DerSpatz/PCB-reflow-solder-table/HeatTable-Base-v0.9/HeatTable-Base-v0.9.kicad_sch

## KiCad design HeatTable-Base-v0.9/HeatTable-Base-v0.9.kicad_sch (2022-12-29)

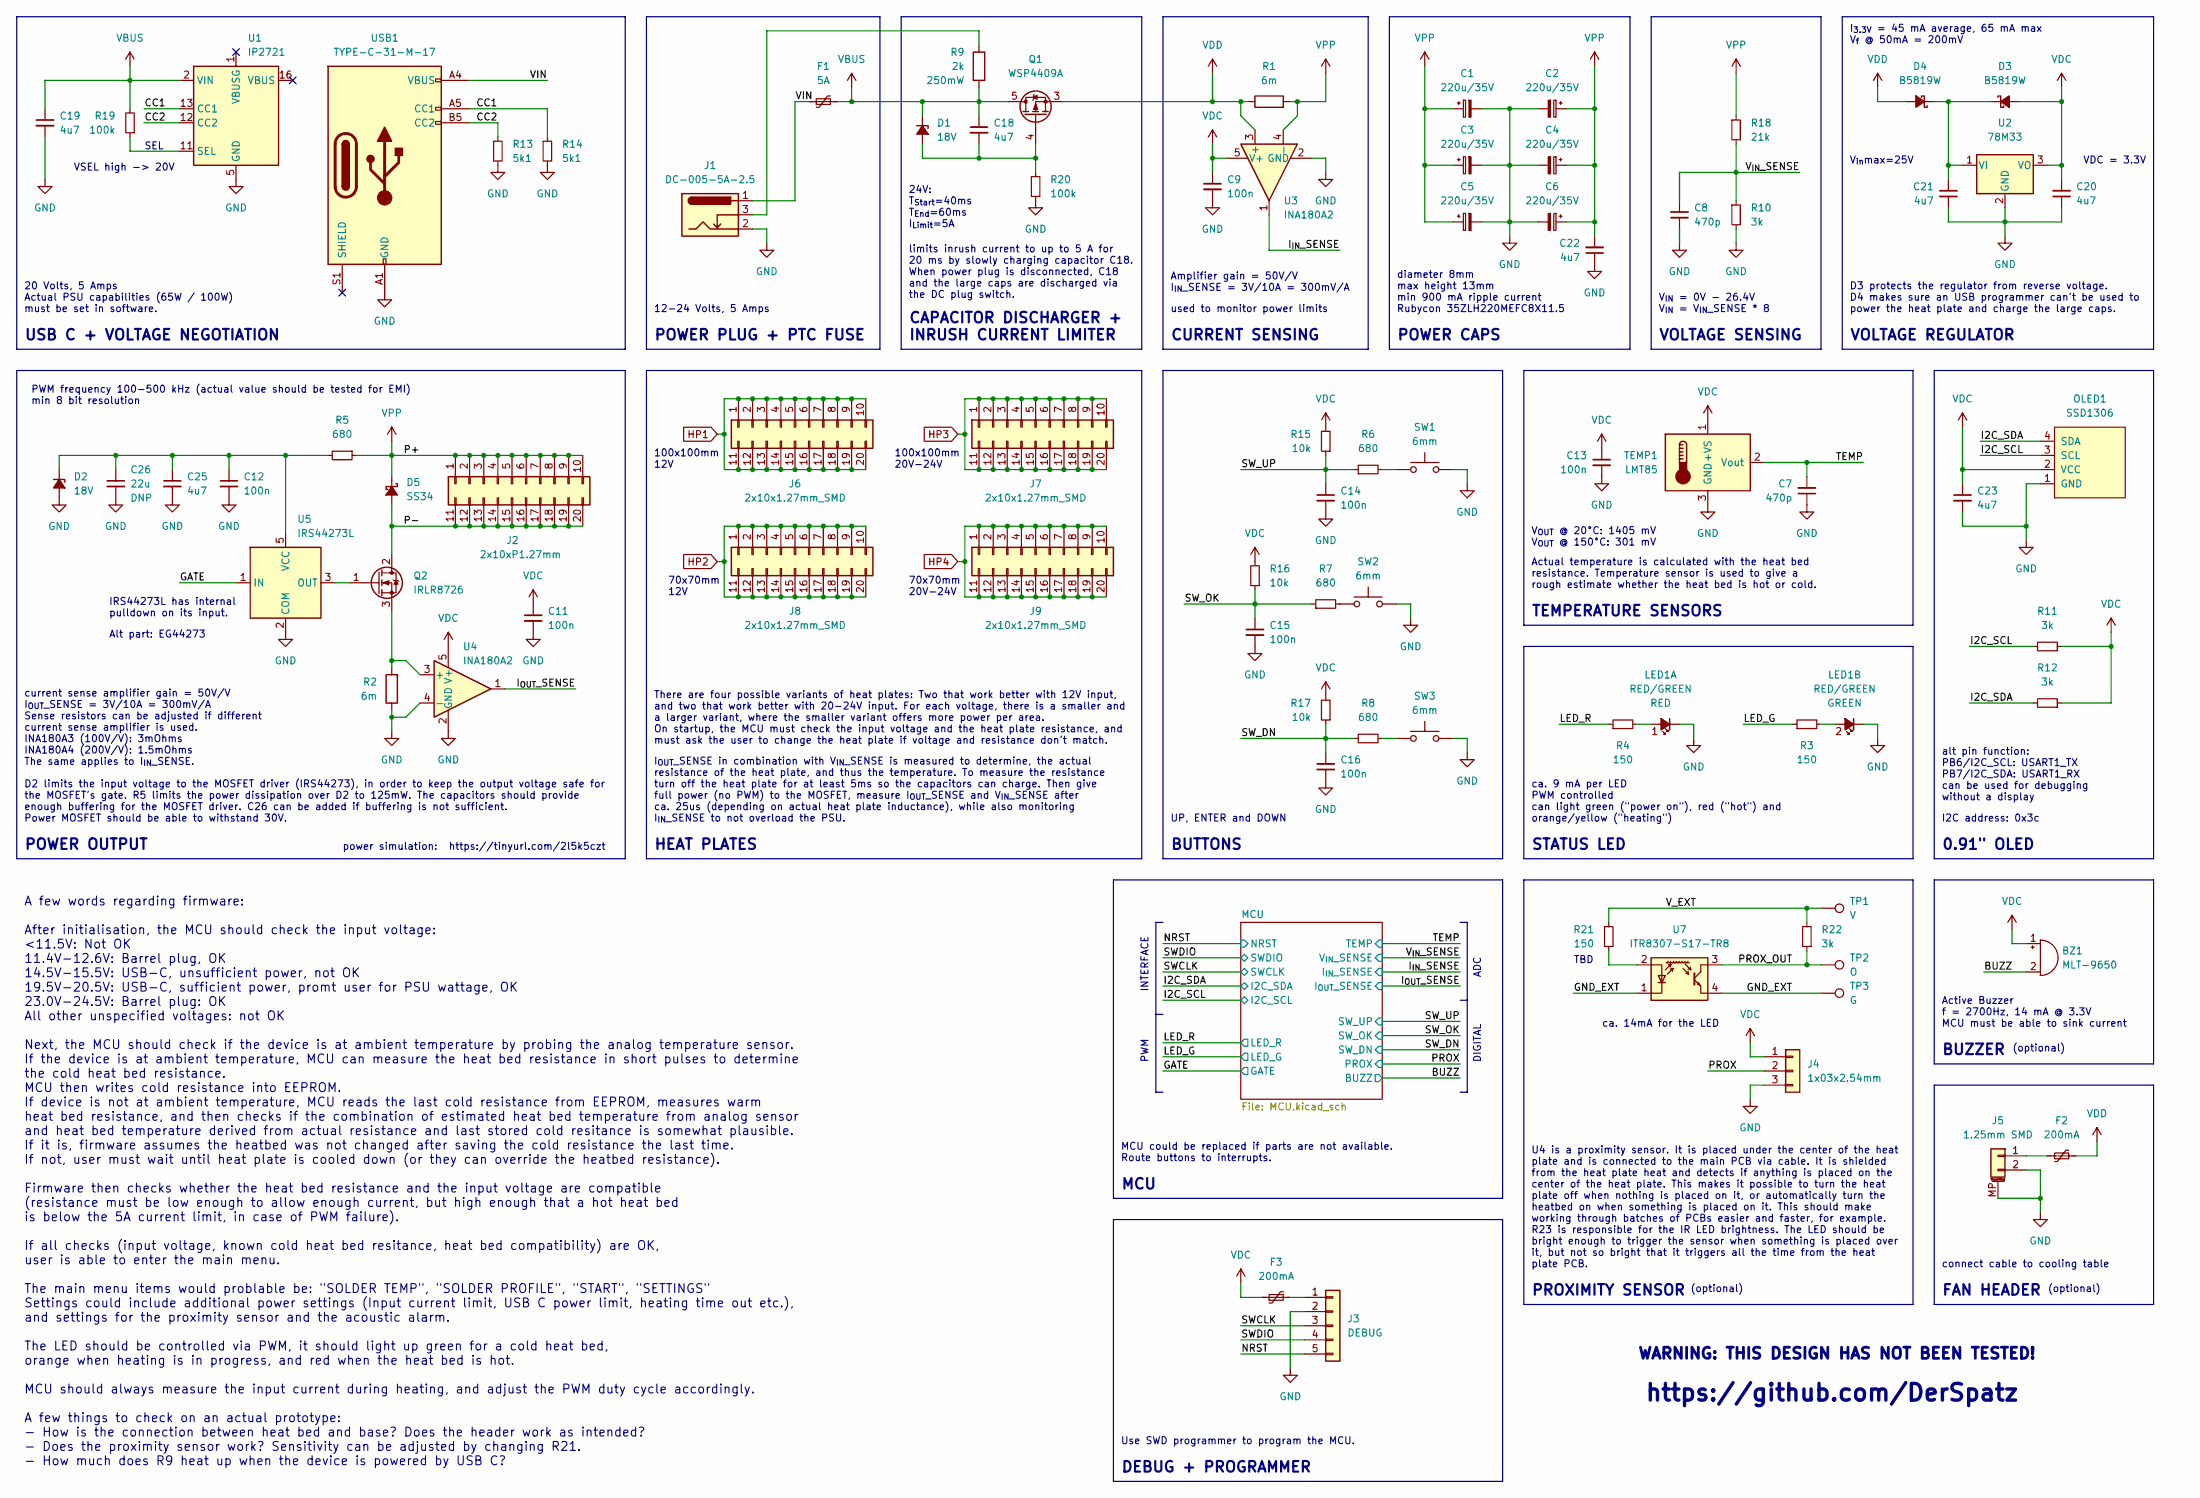
[picture p12: schematic HeatTable-Base-v0.9.kicad_sch]

Parts:
BZ1: MLT-9650; CUI_CMI-9653S-SMT; LCSC Part Number C96127
C1, C2, C3, C4, C5, C6: 220u/35V; CP_Radial_D8.0mm_P3.50mm; LCSC Part Number C107639
C7, C8: 470p; C_0805_2012Metric; LCSC Part Number C1743
C9, C11, C12, C13, C14, C15, C16: 100n; C_0805_2012Metric; LCSC Part Number C49678
C18, C19, C20, C21, C22, C23, C25: 4u7; C_0805_2012Metric; LCSC Part Number C1779
C26: 22u; C_1206_3216Metric; JLCPCB basic part n
D1, D2: 18V; D_SOD-123; JLCPCB basic part n
D3, D4: B5819W; D_SOD-123; LCSC Part Number C8598
D5: SS34; D_SMA; LCSC Part Number C8678
F1: 5A; Fuse_BrightKing_BK30-500; LCSC Part Number C268778
F2, F3: 200mA; Fuse_1206_3216Metric; JLCPCB basic part n
J1: DC-005-5A-2.5; BarrelJack_Horizontal; LCSC Part Number C381115
J2: 2x10xP1.27mm; PinHeader_2x10_P1.27mm_Horizontal_XKB_X1321WR-2x10J-C40D18; LCSC Part Number C2881830
J3: DEBUG; PinHeader_1x05_P2.54mm_Vertical; JLCPCB basic part THT
J4: 1x03x2.54mm; PinHeader_1x03_P2.54mm_Vertical
J5: 1.25mm SMD; Molex_PicoBlade_53398-0271_1x02-1MP_P1.25mm_Vertical; JLCPCB basic part n
J6, J7, J8, J9: 2x10x1.27mm_SMD; PinSocket_2x10_P1.27mm_Vertical_SMD; LCSC Part Number C2684738
LED1: RED/GREEN; LED_Avago_PLCC4_3.2x2.8mm_CW; LCSC Part Number C601677
OLED1: SSD1306; 0.91Inch-OLED-Module; LCSC Part Number C2718488
Q1: WSP4409A; SOIC-8_3.9x4.9mm_P1.27mm; LCSC Part Number C2880527
Q2: IRLR8726; TO-252-2; LCSC Part Number C81137
R1, R2: 6m; R_1206_3216Metric; LCSC Part Number C105369
R3, R4, R21: 150; R_0805_2012Metric; LCSC Part Number C17471
R5, R6, R7, R8: 680; R_0805_2012Metric; LCSC Part Number C17798
R9: 2k; R_1206_3216Metric; JLCPCB basic part y
R10, R11, R12, R22: 3k; R_0805_2012Metric; LCSC Part Number C17661
R13, R14: 5k1; R_0805_2012Metric; LCSC Part Number C27834
R15, R16, R17: 10k; R_0805_2012Metric; LCSC Part Number C17414
R18: 21k; R_0805_2012Metric; LCSC Part Number C17550
R19, R20: 100k; R_0805_2012Metric; LCSC Part Number C149504
SW1, SW2, SW3: 6mm; SW_PUSH_6mm; LCSC Part Number C110153
TEMP1: LMT85; TO-92_Inline; LCSC Part Number C75856
TP1: V; TestPoint_THTPad_D1.7mm_Drill1.0mm
TP2: O; TestPoint_THTPad_D1.7mm_Drill1.0mm
TP3: G; TestPoint_THTPad_D1.7mm_Drill1.0mm
U1: IP2721; TSSOP-16_4.4x5mm_P0.65mm; JLCPCB basic part n
U2: 78M33; SOT-223-3_TabPin2; JLCPCB basic part n
U3, U4: INA180A2; SOT-23-5; JLCPCB basic part n
U5: IRS44273L; SOT-23-5; JLCPCB basic part n
U7: ITR8307-S17-TR8; Everlight_ITR1201SR10AR; LCSC Part Number C81632
USB1: TYPE-C-31-M-17; USB_C_Receptacle_HRO_TYPE-C-31-M-17_Handsoldering; JLCPCB basic part n

Connections:
BUZZ: BZ1.2 (+)
CC1: R14.1, U1.13 (CC1), USB1.A5 (CC1)
CC2: R13.1, U1.12 (CC2), USB1.B5 (CC2)
GATE: U5.1 (IN)
GND: C1.2, C2.2, C3.2, C4.2, C5.2, C6.2, C7.1, C8.1, C9.2, C11.2, C12.2, C13.2, C14.2, C15.2, C16.2, C19.2, C20.1, C21.2, C22.1, C23.2, C25.2, C26.2, D2.2 (A), J1.2, J3.2, J4.3, J5.2, J5.MP (MountPin), LED1.2 (K1), LED1.4 (K2), OLED1.1 (GND), R2.1, R10.2, R13.2, R14.2, R20.2, SW1.2, SW2.2, SW3.2, TEMP1.3 (GND), U1.5 (GND), U2.2 (GND), U3.2 (GND), U4.2 (GND), U4.4 (-), U5.2 (COM), USB1.A1 (GND), USB1.A12 (GND), USB1.B1 (GND), USB1.B12 (GND)
GND_EXT: TP3.1, U7.1 (K), U7.4
HP1: J6.1, J6.2, J6.3, J6.4, J6.5, J6.6, J6.7, J6.8, J6.9, J6.10, J6.11, J6.12, J6.13, J6.14, J6.15, J6.16, J6.17, J6.18, J6.19, J6.20
HP2: J8.1, J8.2, J8.3, J8.4, J8.5, J8.6, J8.7, J8.8, J8.9, J8.10, J8.11, J8.12, J8.13, J8.14, J8.15, J8.16, J8.17, J8.18, J8.19, J8.20
HP3: J7.1, J7.2, J7.3, J7.4, J7.5, J7.6, J7.7, J7.8, J7.9, J7.10, J7.11, J7.12, J7.13, J7.14, J7.15, J7.16, J7.17, J7.18, J7.19, J7.20
HP4: J9.1, J9.2, J9.3, J9.4, J9.5, J9.6, J9.7, J9.8, J9.9, J9.10, J9.11, J9.12, J9.13, J9.14, J9.15, J9.16, J9.17, J9.18, J9.19, J9.20
I2C_SCL: OLED1.3 (SCL), R11.2
I2C_SDA: OLED1.4 (SDA), R12.2
I_{IN}_SENSE: U3.1
I_{OUT}_SENSE: U4.1
LED_G: R3.1
LED_R: R4.1
NRST: J3.5
unnamed: C12.1, C25.1, C26.1, D2.1 (K), R5.2, U5.5 (VCC)
unnamed: C18.2, D1.2 (A), Q1.4 (G), R20.1
unnamed: C21.1, D3.1 (K), D4.1 (K), U2.1 (VI)
unnamed: F2.1, J5.1
unnamed: F3.2, J3.1
unnamed: J1.3, R9.1
unnamed: LED1.1 (A1), R4.2
unnamed: LED1.3 (A2), R3.2
unnamed: Q2.1 (G), U5.3 (OUT), U5.4 (OUT)
unnamed: Q2.3 (S), R2.2, U4.3 (+)
unnamed: R6.2, SW1.1
unnamed: R7.2, SW2.1
unnamed: R8.2, SW3.1
unnamed: R19.1, U1.11 (SEL)
unnamed: R21.2, U7.2 (A)
unnamed: U1.3 (NC), U1.4 (NC), U1.6 (TST1), U1.7 (TST2), U1.8 (TST3), U1.9 (NC), U1.10 (NC), U1.14 (NC), U1.15 (NC)
P-: D5.2 (A), J2.11, J2.12, J2.13, J2.14, J2.15, J2.16, J2.17, J2.18, J2.19, J2.20, Q2.2 (D)
PROX: J4.2
PROX_OUT: R22.1, TP2.1, U7.3
SWCLK: J3.3
SWDIO: J3.4
SW_DN: C16.1, R8.1, R17.1
SW_OK: C15.1, R7.1, R16.1
SW_UP: C14.1, R6.1, R15.1
TEMP: C7.2, TEMP1.2 (Vout)
VBUS: C18.1, C19.1, D1.1 (K), F1.2, Q1.5 (D), Q1.6 (D), Q1.7 (D), Q1.8 (D), R9.2, R19.2, U1.2 (VIN)
VDC: BZ1.1 (-), C9.1, C11.1, C13.1, C20.2, C23.1, D3.2 (A), F3.1, J4.1, OLED1.2 (VCC), R11.1, R12.1, R15.2, R16.2, R17.2, TEMP1.1 (+VS), U2.3 (VO), U3.5 (V+), U4.5 (V+)
VDD: D4.2 (A), F2.2, Q1.1 (S), Q1.2 (S), Q1.3 (S), R1.1, U3.3 (+)
VIN: F1.1, J1.1, USB1.A4 (VBUS), USB1.A9 (VBUS), USB1.B4 (VBUS), USB1.B9 (VBUS)
VPP: C1.1, C2.1, C3.1, C4.1, C5.1, C6.1, C22.2, D5.1 (K), J2.1, J2.2, J2.3, J2.4, J2.5, J2.6, J2.7, J2.8, J2.9, J2.10, R1.2, R5.1, R18.1, U3.4 (-)
V_EXT: R21.1, R22.2, TP1.1
V_{IN}_SENSE: C8.2, R10.1, R18.2

Notes on the sheet:
power simulation:
IRS44273L has internal pulldown on its input.
Actual temperature is calculated with the heat bed resistance. Temperature sensor is used to give a rough estimate whether the heat bed is hot or cold.
V_{IN} = 0V - 26.4V V_{IN} = V_{IN}_SENSE * 8
BUTTONS
100x100mm 12V
diameter 8mm max height 13mm min 900 mA ripple current Rubycon 35ZLH220MEFC8X11.5
DIGITAL
ca. 9 mA per LED PWM controlled can light green ("power on"), red ("hot") and orange/yellow ("heating")
POWER CAPS
WARNING: THIS DESIGN HAS NOT BEEN TESTED!
24V: T_{Start}=40ms T_{End}=60ms I_{Limit}=5A
CURRENT SENSING
Active Buzzer f = 2700Hz, 14 mA @ 3.3V MCU must be able to sink current
VSEL high -> 20V
INTERFACE
FAN HEADER
https://tinyurl.com/2l5k5czt
POWER OUTPUT
I_{3.3V} = 45 mA average, 65 mA max V_{f} @ 50mA = 200mV
PROXIMITY SENSOR
DEBUG + PROGRAMMER
alt pin function: PB6/I2C_SCL: USART1_TX PB7/I2C_SDA: USART1_RX can be used for debugging without a display
(optional)
0.91" OLED
connect cable to cooling table
PWM frequency 100-500 kHz (actual value should be tested for EMI) min 8 bit resolution
70x70mm 20V-24V
STATUS LED
ADC
used to monitor power limits
Use SWD programmer to program the MCU.
current sense amplifier gain = 50V/V I_{OUT}_SENSE = 3V/10A = 300mV/A Sense resistors can be adjusted if different current sense amplifier is used. INA180A3 (100V/V): 3mOhms INA180A4 (200V/V): 1.5mOhms The same applies to I_{IN}_SENSE.
POWER PLUG + PTC FUSE
I_{OUT}_SENSE in combination with V_{IN}_SENSE is measured to determine, the actual resistance of the heat plate, and thus the temperature. To measure the resistance turn off the heat plate for at least 5ms so the capacitors can charge. Then give full power (no PWM) to the MOSFET, measure I_{OUT}_S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
Alt part: EG44273
limits inrush current to up to 5 A for 20 ms by slowly charging capacitor C18. When power plug is disconnected, C18 and the large caps are discharged via the DC plug switch.
UP, ENTER and DOWN
ca. 14mA for the LED
U4 is a proximity sensor. It is placed under the center of the heat plate and is connected to the main PCB via cable. It is shielded from the heat plate heat and detects if anything is placed on the center of the heat plate. This makes it possible to turn the heat plate off when nothing is placed o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
TBD
D2 limits the input voltage to the MOSFET driver (IRS44273), in order to keep the output voltage safe for the MOSFET's gate. R5 limits the power dissipation over D2 to 125mW. The capacitors should provide enough buffering for the MOSFET driver. C26 can be added if buffering is not sufficient. Power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
V_{in}max=25V
V_{OUT} @ 20°C: 1405 mV V_{OUT} @ 150°C: 301 mV
PWM
VOLTAGE SENSING
BUZZER
D3 protects the regulator from reverse voltage. D4 makes sure an USB programmer can't be used to power the heat plate and charge the large caps.
I2C address: 0x3c
A few words regarding firmware: After initialisation, the MCU should check the input voltage: <11.5V: Not OK 11.4V-12.6V: Barrel plug, OK 14.5V-15.5V: USB-C, unsufficient power, not OK 19.5V-20.5V: USB-C, sufficient power, promt user for PSU wattage, OK 23.0V-24.5V: Barrel plug: OK All other unspec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
VDC = 3.3V
100x100mm 20V-24V
https://github.com/DerSpatz
There are four possible variants of heat plates: Two that work better with 12V input, and two that work better with 20-24V input. For each voltage, there is a smaller and a larger variant, where the smaller variant offers more power per area. On startup, the MCU must check the input voltage and the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
70x70mm 12V
USB C + VOLTAGE NEGOTIATION
VOLTAGE REGULATOR
CAPACITOR DISCHARGER + INRUSH CURRENT LIMITER
SEL
20 Volts, 5 Amps Actual PSU capabilities (65W / 100W) must be set in software.
12-24 Volts, 5 Amps
MCU
MCU could be replaced if parts are not available. Route buttons to interrupts.
HEAT PLATES
TEMPERATURE SENSORS
Amplifier gain = 50V/V I_{IN}_SENSE = 3V/10A = 300mV/A
