DerSpatz/PCB-reflow-solder-table/HeatTable-Base-v0.9/MCU.kicad_sch

## KiCad design HeatTable-Base-v0.9/MCU.kicad_sch (2022-09-21)

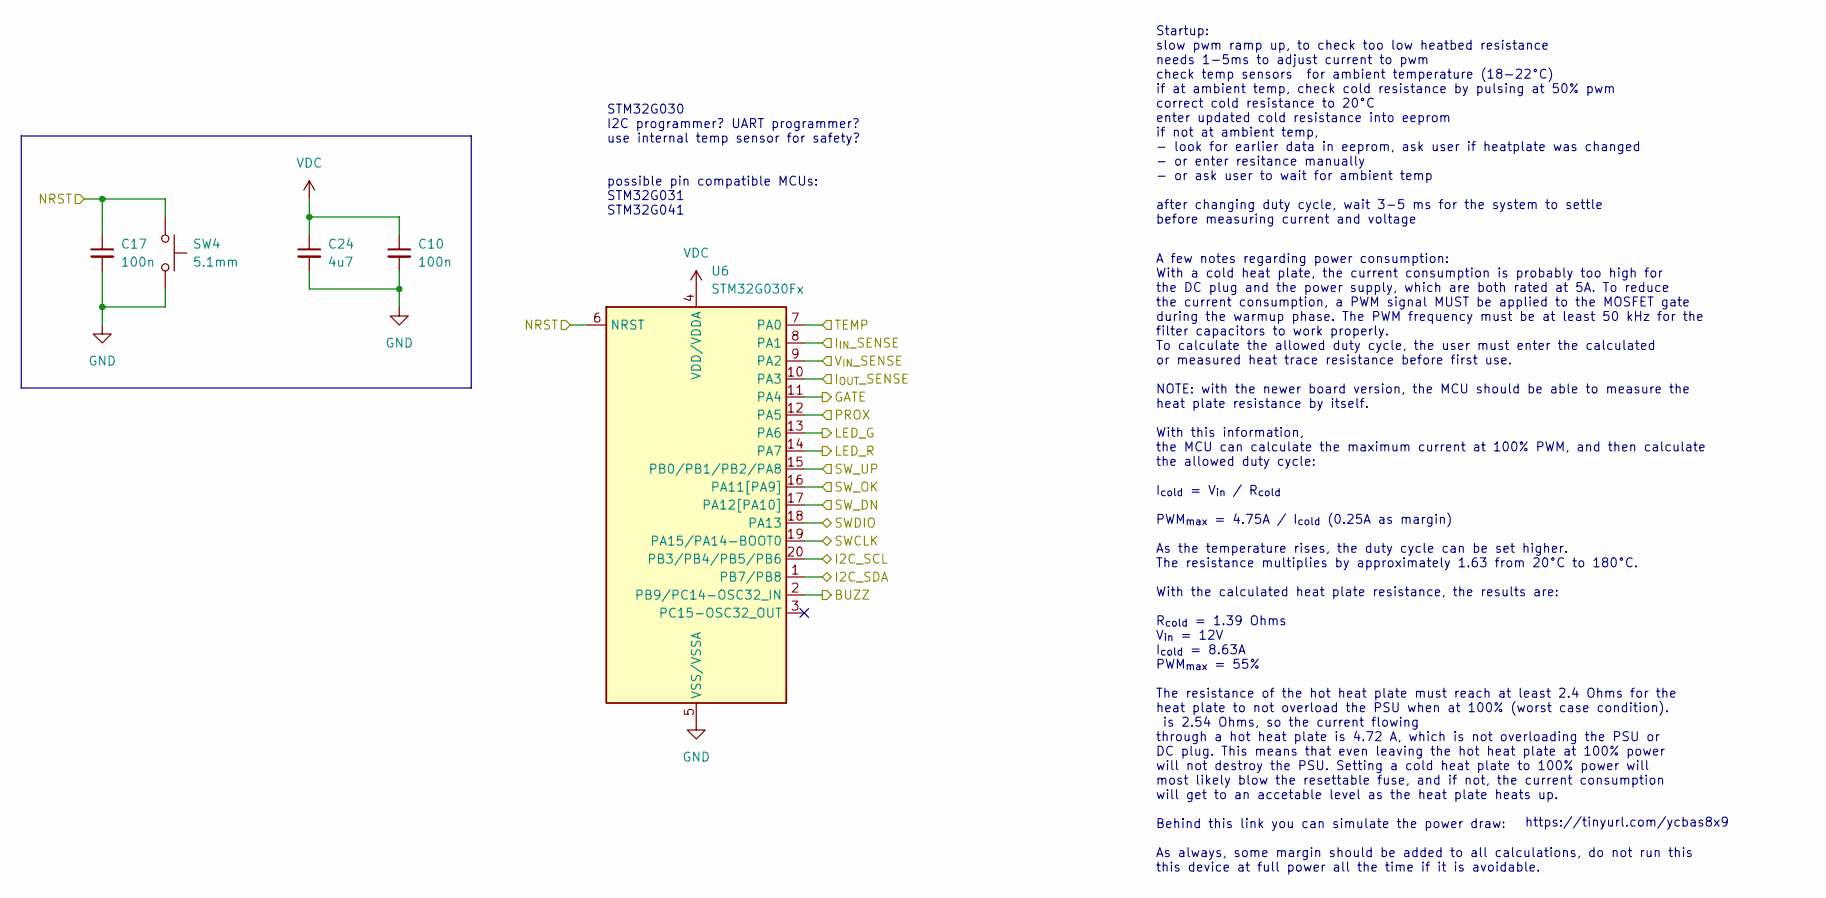
[picture p13: schematic MCU.kicad_sch]

Parts:
C10, C17: 100n; C_0805_2012Metric; LCSC Part Number C49678
C24: 4u7; C_0805_2012Metric; LCSC Part Number C1779
SW4: 5.1mm; SW_SPST_SKQG_WithStem; LCSC Part Number C318884
U6: STM32G030Fx; TSSOP-20_4.4x6.5mm_P0.65mm; LCSC Part Number C724040

Connections:
BUZZ: U6.2 (PB9/PC14-OSC32_IN)
GATE: U6.11 (PA4)
GND: C10.2, C17.2, C24.2, SW4.2, U6.5 (VSS/VSSA)
I2C_SCL: U6.20 (PB3/PB4/PB5/PB6)
I2C_SDA: U6.1 (PB7/PB8)
I_{IN}_SENSE: U6.8 (PA1)
I_{OUT}_SENSE: U6.10 (PA3)
LED_G: U6.13 (PA6)
LED_R: U6.14 (PA7)
NRST: C17.1, SW4.1, U6.6 (NRST)
PROX: U6.12 (PA5)
SWCLK: U6.19 (PA15/PA14-BOOT0)
SWDIO: U6.18 (PA13)
SW_DN: U6.17 (PA12[PA10])
SW_OK: U6.16 (PA11[PA9])
SW_UP: U6.15 (PB0/PB1/PB2/PA8)
TEMP: U6.7 (PA0)
VDC: C10.1, C24.1, U6.4 (VDD/VDDA)
V_{IN}_SENSE: U6.9 (PA2)

Notes on the sheet:
https://tinyurl.com/ycbas8x9
A few notes regarding power consumption: With a cold heat plate, the current consumption is probably too high for the DC plug and the power supply, which are both rated at 5A. To reduce the current consumption, a PWM signal MUST be applied to the MOSFET gate during the warmup phase. The PWM frequen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
Startup: slow pwm ramp up, to check too low heatbed resistance needs 1-5ms to adjust current to pwm check temp sensors for ambient temperature (18-22°C) if at ambient temp, check cold resistance by pulsing at 50% pwm correct cold resistance to 20°C enter updated cold resistance into eeprom if not a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
STM32G030 I2C programmer? UART programmer? use internal temp sensor for safety?
possible pin compatible MCUs: STM32G031 STM32G041
